tambechristian/Zulu_A7/Zulu_Altium_VS_Code/docs/power_budget.md

# Zulu A7 power budget

Source: zulu_a7.sch as imported (Imported zulu_a7.PrjPcb), datasheets in Datasheet/. Generated by tools/power_budget.py with --fpga-int 250 --fpga-aux 15 --fpga-io 30 --header 0.

Power comes in as USB VBUS into U8, a TI bq24232 charger and power-path manager whose OUT regulates VU at 4.4 V and caps the input at 495 mA, charging the LiPo on X4 at up to 244 mA with what is left (the battery supplements peaks and runs the board alone at VBAT - 60 mV). The +5V-INPUT pin with D2 and D3 went on 2026-09-09, so the charger is the only way in. VU feeds three fixed SC189 bucks, U5 (3.3 V), U6 (1.8 V) and U7 (1.0 V), 1.5 A each at 2.5 MHz, enables tied to VU, so all three rails soft-start together when VU appears; UG483 requires no order between VCCINT, VCCAUX and VCCO.

## VCC3V3 = 3.3 V on U5 SC189Z (1.5 A)

| Consumer | typ mA | max mA | Source |
|---|---:|---:|---|
| U2 FT2232HL core via VREGIN (Icc1) | 70 | 70 | FT2232H DS Table 5.2, 70 mA |
| U2 FT2232HL USB PHY (Iccphy, high speed) | 30 | 60 | FT2232H DS Table 5.4, 30 typ / 60 max |
| U2 FT2232HL VCCIO switching | 10 | 20 | ASSUMED, 3.3 V I/O cells at JTAG/UART rates |
| U3 SDRAM AS4C32M16SB-7TCN | 100 | 150 | IDD1 110, IDD4 120, IDD5 150 (refresh), IDD2N 80 standby (Rev 1.4); the -6TIN was 120/124/160 until 2026-09-08 |
| U4 W25Q128JV flash (quad read 104 MHz / program) | 12 | 25 | ICC3 12 typ 20 max; ICC5 program 25 max |
| X3 microSD card | 60 | 200 | SD spec: ~60 typ, 200 max at 3.3 V for a high-speed card |
| U10 93LC46B EEPROM | 1 | 2 | read 1 mA, write 2 mA max |
| Q1 ECS-3225SMV 12 MHz oscillator | 6 | 10 | ECS-3225SMV sheet: 6 typ / 10 mA max at 15 pF (was ASEM1 7/15 until 2026-09-08) |
| U1 VCCO banks 0/14/16/34/35 (28 balls) static | 5 | 5 | DS181 ICCOQ, about 1 mA per bank |
| U1 VCCO dynamic (SDRAM bus, header, LED sink path) | 30 | 90 | ASSUMED; about 1.6 mA per toggling pin at 100 MHz, 10 pF |
| LD0 RGB (R80 33, R81 330, R82 33) + LD1/LD2 (330) + LD5 (680) | 8 | 22 | VF from the Everlight 19-337 sheet: red 2.05 typ / 2.4 max, green and blue 3.2 typ / 3.7 max V (VS NRD8 was 2.0-2.4 / 3.3-3.8 until 2026-09-08) |
| pull-ups when driven low (6 x 4.7k, 12 x 10k) | 2 | 8 | R1, R2, R6, R7, R34, R35, R90-R99, R19, R20, R23 |
| J1 Pmod pins 6/12 and X2 pin 18 +3.3V to header | 0 | 0 | external, user allowance |
| **Total** | **334** | **662** | channel limit 1500 mA |
| Headroom | 1166 | 838 | ok |

## VCC1V8 = 1.8 V on U6 SC189L (1.5 A)

| Consumer | typ mA | max mA | Source |
|---|---:|---:|---|
| U1 VCCAUX quiescent (H13, J13) | 22 | 22 | DS181 Table 7, ICCAUXQ 22 mA |
| U1 VCCAUX dynamic (MMCM, config, I/O aux) | 15 | 30 | ASSUMED; Vivado report_power |
| U1 VCCADC via L7 (XADC on, AIN15/AIN16 used) | 12 | 25 | DS181 ICCADC 25 mA max |
| U1 VCCBATT (C9) | 0 | 0 | tied to VCC1V8, no battery: negligible |
| X2 pin 19 +1.8V to header | 0 | 0 | external, user allowance |
| **Total** | **49** | **77** | channel limit 1500 mA |
| Headroom | 1451 | 1423 | ok |

## VCC1V0 = 1.0 V on U7 SC189A (1.5 A)

| Consumer | typ mA | max mA | Source |
|---|---:|---:|---|
| U1 VCCINT quiescent (6 balls) | 95 | 95 | DS181 Table 7, XC7A35T ICCINTQ 95 mA typ at 85 C junction |
| U1 VCCINT dynamic | 250 | 250 | ASSUMED design load; replace with Vivado report_power |
| U1 VCCBRAM (2 balls) quiescent + dynamic | 22 | 22 | DS181 ICCBRAMQ 2 mA; dynamic assumed |
| X2 pin 20 +1.0V to header | 0 | 0 | external, user allowance |
| **Total** | **367** | **367** | channel limit 1500 mA |
| Headroom | 1133 | 1133 | ok |

## Power-on requirement (DS181 Table 9, XC7A35T)

The supplies must deliver the quiescent current plus an inrush allowance while the FPGA powers up, before anything is configured:

| Rail | Requirement | This board | ok |
|---|---|---:|---|
| VCC1V0 | ICCINTQ + 120 + ICCBRAMQ + 60 | 277 mA | ok (channel 1500 mA) |
| VCC1V8 | ICCAUXQ + 40 | 62 mA | ok (channel 1500 mA) |
| VCC3V3 | ICCOQ + 40 mA per bank x 5 banks, plus the rest of the rail at rest | 362 mA | ok (channel 1500 mA) |

## Input from USB

VU = 4.40 V, the bq24232 OUT regulation while USB is present (the charger is an LDO from the 5 V port). Input power per rail is Vout x Iout / efficiency, efficiency read from the SC189 datasheet's SOT23-5 curves at 5 V in (p6).

| Rail | typ W in | max W in | efficiency |
|---|---:|---:|---:|
| VCC3V3 | 1.22 | 2.43 | 90% |
| VCC1V8 | 0.11 | 0.18 | 78% |
| VCC1V0 | 0.45 | 0.45 | 81% |
| **USB current at 4.40 V** | **409 mA** | **697 mA** | bq24232 input limit 495 mA; USB allows 500 mA configured, 100 mA before enumeration |

- Typical use draws about 409 mA through the charger: inside the 495 mA input limit, leaving about 86 mA of the 244 mA charge current for the battery while the board runs; the full 244 mA flows when the board idles.
- The simultaneous worst case wants about 697 mA: over the charger's input limit, so the excess comes from the battery in supplement mode; with no battery fitted VU sags to the DPPM point and the board browns out under that load.
- All three rails start as soon as VBUS appears and the FPGA configures from flash immediately, so the board is above the 100 mA unconfigured limit before the FT2232H enumerates. Hosts tolerate this in practice; FT-PWREN# reaches the FPGA (P17) if you ever want to hold heavy loads off until enumeration.
- VU, which is the charger's OUT, carries C78 (10 uF) plus the three SC189 input caps C147-C149 (10 uF each; the datasheet wants at least 4.7 uF effective at every VIN pin): 40 uF nominal, roughly 25 uF effective at 5 V. The USB 2.0 limit for bulk capacitance seen at attach is 10 uF (50 uC of inrush). The bq24232 sits between the port and that capacitance and limits inrush by its start-up sequence; the datasheet allows 4.7-47 uF on OUT, so the 40 uF is inside its window. On battery alone the SC189 3.3 V buck keeps regulation down to about 3.45 V of battery (VU = VBAT - 60 mV); the 1.8 V and 1.0 V rails run to the pack's cut-off.

## Thermal, still air, first order

| Part | P typ W | P max W | thJA C/W | rise typ C | rise max C |
|---|---:|---:|---:|---:|---:|
| U1 XC7A35T CPG236 | 0.57 | 0.82 | 24.8 | 14 | 20 |
| U5 SC189Z (1.5 A) for VCC3V3 | 0.12 | 0.24 | 90 | 11 | 22 |
| U6 SC189L (1.5 A) for VCC1V8 | 0.02 | 0.04 | 90 | 2 | 4 |
| U7 SC189A (1.5 A) for VCC1V0 | 0.09 | 0.09 | 90 | 8 | 8 |
| U2 FT2232HL (DS Table 5.7) | 0.36 | 0.49 | 37.66 | 14 | 19 |
| U3 SDRAM (thJA assumed) | 0.33 | 0.53 | 45 | 15 | 24 |
| U8 bq24232 (DS 7.4, path + charge) | 0.36 | 0.61 | 44.5 | 16 | 27 |

The FPGA stays well under its 85 C commercial junction limit. The SOT23-5 regulators are the warm parts now: the 3.3 V one dissipates about 0.12 W typical and up to 0.25 W at the datasheet maxima, which at the datasheet's 90 C/W (SOT23-5 on a 10x10 mm 2-layer 1 oz test board) is an 11-22 C rise. Figure 3 of the SC189 sheet rates the SOT23-5 for the full 1.5 A at 3.3 V out up to about 65 C ambient, so no derating applies here. Give the GND pin and the LX/VOUT copper a pour anyway; the 2x2 mm MLPD-UT6 version (SC189xULTRT, 60 C/W) is the fallback if the board must run hot.

## Findings

1. **No rail is near its regulator limit any more.** Each SC189 gives 1.5 A; VCC3V3 uses under a quarter of that in typical use and under half at the datasheet maxima, VCC1V0 a quarter, VCC1V8 a twentieth. The header and Pmod +3.3V pins can take several hundred milliamps when the board runs from USB with a charged battery supplementing.
2. **The bq24232 input limit is the ceiling on USB.** The charger holds the port at 495 mA whatever the board does; typical use fits, the datasheet-maximum case is served by the battery in supplement mode, the only other source now that the +5V-INPUT pin is gone.
3. **VCC1V8 is lightly loaded**, well under 100 mA even with the XADC running.
4. **USB alone covers typical use** at about 409 mA through the charger, with about 86 mA left for charging. The simultaneous worst case (697 mA) needs the battery in supplement mode; there is no other input since the +5V-INPUT pin went on 2026-09-09.
5. **Green and blue of LD0 may not light.** Their forward voltage is 3.2 V typical and 3.7 V maximum per the Everlight 19-337 sheet (3.3-3.8 V on the VS NRD8 it replaced on 2026-09-08), and the FPGA sinks them from a 3.3 V supply through 33 ohm, leaving no headroom; only the red (2.0-2.4 V) has margin. Expect dim or dark green/blue unless the parts fall at the low end of VF. Not a power problem, but it fell out of the LED current estimate.
6. **Sequencing is gone by design.** Every SC189 EN is tied to VU, so the three rails soft-start together. UG483 recommends VCCINT, VCCBRAM, VCCAUX, VCCO but requires no order and allows simultaneous ramps. The old LTC3569 EN_BIAS network went with it; it was copied from the Cmod A7 rev B, which Digilent shipped, so it evidently works in practice, but it holds the gated enables at 0.65-0.8 V, below the LTC3569 guaranteed 1.2 V high level, and Q3 pulls them low once VCC1V0 is up.
7. **The rails carry far more capacitance than the SC189 datasheet allows at start-up.** Page 19 says total output capacitance should not exceed 30 uF to avoid start-up problems: the fixed 100 us soft-start (current limit stepped 20/25/40/100 % of 2 A, 20 us each) delivers only 40-75 uC, after which the part runs at its 2 A limit and, after 32 cycles over the limit, folds back to 50-110 mA (Figure 5) until the load falls below that. UG483 Table 2-2 requires 100 uF on VCCINT, 47 uF on VCCBRAM, 47 uF on VCCAUX and 47 uF per VCCO group for this FPGA, so the sheet has 165 uF nominal on VCC1V0, 167 uF on VCC3V3 and 72 uF on VCC1V8 (about 150, 90 and 60 uF after DC bias), needing 150, 300 and 110 uC. Every rail therefore finishes its ramp in current limit or foldback, and a load that draws more than the foldback current before the rail is up (the FPGA's VCCINT power-on current is about 200 mA, the FT2232H on 3.3 V about 70 mA) could hold it down. A newer Cmod A7 revision runs three SC189s into this same FPGA (the source is the user's photo of that board; the rev B.1 schematic on disk still shows the LTC3569), which suggests it works in practice, but it is the one datasheet limit this design does not meet: scope the three rails at power-on on the first board. If a rail hangs, the fixes are a regulator with a soft-start pin in the same role (TPS62130/TPS62823 class) or staggering the enables with RC delays so the rails do not all draw from VU at once.
