tambechristian/Zulu_A7/Altium_backup/docs/sdram_bus_widths.md

# SDRAM bus on L3/L4 — width, spacing and what the bus actually needs, 2026-09-14

**Status: APPLIED AND PROVEN, 2026-09-15.** Three analyses (signal integrity,
routability, fab and yield), each adversarially refuted, then a judge — 1.28 M tokens, all
numbers below survived refutation from the files or are marked general knowledge. The
implementation is `SetSdramRules` in `tools/ZuluSetup.pas`; `tools/verify_widths.py` carries
the targets.

## What the bus needs — and it is not 50 Ω
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
