tambechristian/Zulu_A7/Zulu_Altium_VS_Code_HDI_Optimized/jlcpcb_hdi_optimized_cost_vs_regular.png

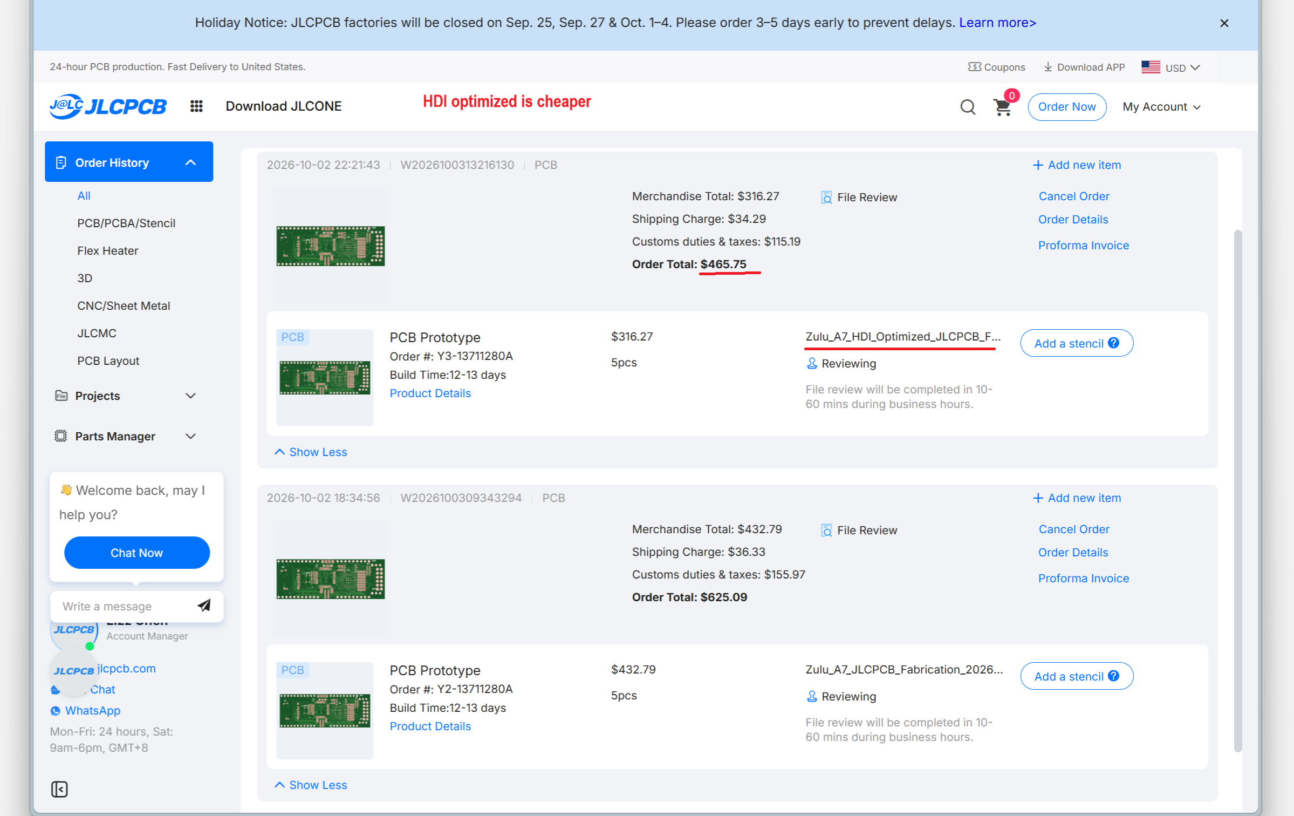
Zulu_Altium_VS_Code_HDI_Optimized/jlcpcb_hdi_optimized_cost_vs_regular.png
