tambechristian/Zulu_A7/Zulu_Altium_VS_Code_HDI_Optimized/pcbway_cost.png

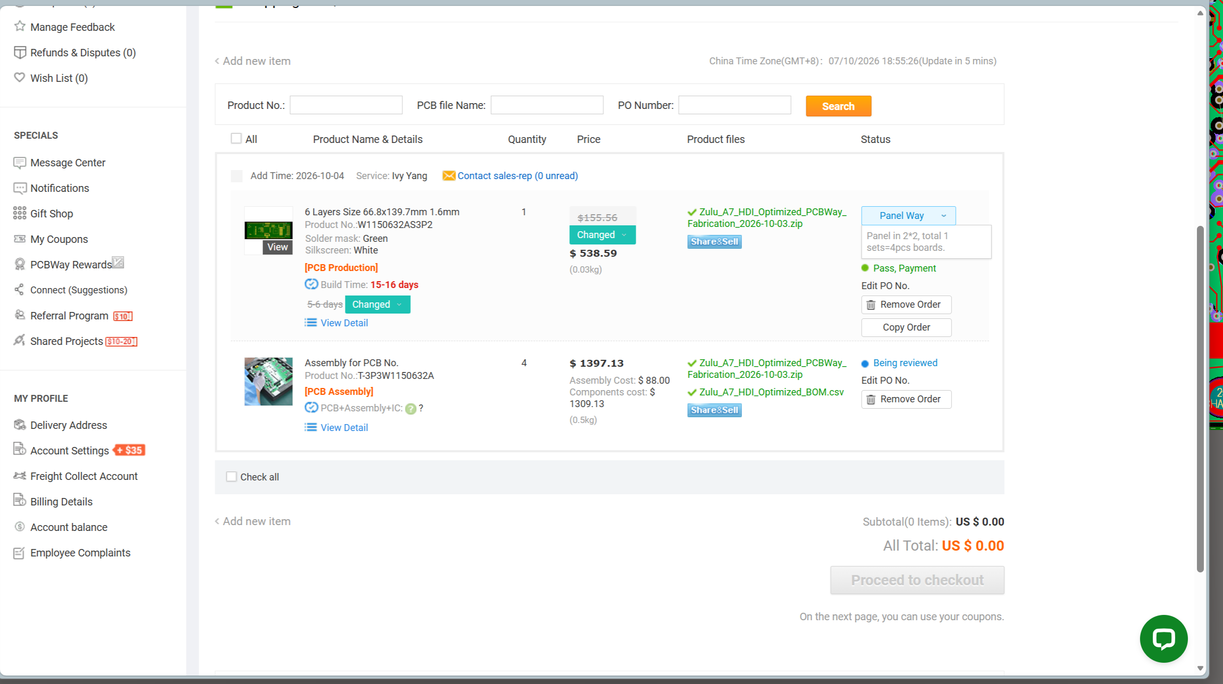
Zulu_Altium_VS_Code_HDI_Optimized/pcbway_cost.png
