tambechristian/Zulu_A7/Claude_Fable/tools/plane_islands.py

# -*- coding: utf-8 -*-
"""Does an inner plane pour actually reach every through object of its net?

    python tools/plane_islands.py [board.brd] [--layer 2] [--net GND]
    python tools/plane_islands.py zulu_a7.brd --layer 5 --net VCC3V3

WHY. check_connectivity treats a <polygonpour> on L2 or L5 as SOLID: every via
and plated pad of the net that crosses the layer is taken as one piece. That is
what a plane is for, but it is an assumption, and two things on this board can
break it. Seven signals were routed ON the plane layers with laser vias, and
every one of their traces is a slot cut through the copper. And the BGA moat
puts foreign vias at 0.39 mm centres, whose antipads overlap into a wall. A via
of the plane's own net standing inside such a slot or wall has copper around it
that is not the plane. Fusion's DRC reports exactly that as an "Air Wire" that
Ratsnest never showed, which is where the 63-against-41 gap came from.

HOW. Rasterise the pour outline. A pour centreline must keep `isolate` from
every foreign object and the copper it lays is `width` wide, so the region a
centreline may occupy is everything at least isolate + width/2 from foreign
copper. Flood that region into pieces. An own via or plated pad is reached by a
piece if a cell of that piece lies within its land radius + width/2 of it, so
the pour's copper edge touches the land. Report every own object that no piece
reaches (isolated) and every one reached only by a piece other than the main
plane (on an island).

Foreign plated pads are modelled at their full drawn diameter on the inner
layer, which is conservative: Eagle draws only the restring annulus there.
"""

import collections
import io
import math
import os
import re
import sys

sys.path.insert(0, os.path.dirname(os.path.abspath(__file__)))
import escape as E   # noqa: E402
import geom as G     # noqa: E402

ROOT = os.path.dirname(os.path.dirname(os.path.abspath(__file__)))
RASTER = 0.05


def arg(name, default):
    if name in sys.argv:
        return sys.argv[sys.argv.index(name) + 1]
    return default


def via_span(attrs):
    first, last = (int(v) for v in attrs.get("extent", "1-16").split("-"))
    return min(first, last), max(first, last)


def analyse(board, layer, net, log=print, grid=None):
    """Raster the pour; report. With `grid` = (x0, y0, W, H) the raster is
    laid on the caller's grid (RASTER step) so its labels can be used as a
    routing layer. Returns a dict, or None if the net has no pour there:
        isolated, islanded   lists of (kind, x, y)
        reached              set of (x, y) rounded to 3 places, own objects
                             the main piece reaches
        label, main, W, H, x0, y0, S     the raster itself
    """
    sig = re.search(r"<signals>(.*)</signals>", board, re.S).group(1)
    signals = {}
    for m in re.finditer(r'<signal name="([^"]+)"[^>]*>(.*?)</signal>', sig, re.S):
        signals[m.group(1)] = m.group(2)
    own_body = signals.get(net, "")
    pm = re.search(r'<polygonpour layer="%d"([^>]*)>(.*?)</polygonpour>'
                   % layer, own_body, re.S)
    if not pm:
        log("  ****  %s has no pour on layer %d" % (net, layer))
        return None
    attrs = dict(re.findall(r'(\w+)="([^"]*)"', pm.group(1)))
    isolate = float(attrs.get("isolate", "0.25"))
    width = float(attrs.get("width", "0.1524"))
    verts = [(float(x), float(y)) for x, y in
             re.findall(r'<vertex x="([-\d.]+)" y="([-\d.]+)"', pm.group(2))]
    x0, x1 = min(v[0] for v in verts), max(v[0] for v in verts)
    y0, y1 = min(v[1] for v in verts), max(v[1] for v in verts)
    keep = isolate + width / 2.0

    # own entries: (kind, key x, key y, land radius, sample points). A pad or
    # via is one sample at its centre; an own wire on the layer is sampled
    # along its length, keyed by its first point, because Fusion pours the
    # copper straight over its own wires and they become part of the plane.
    circles, rects, own = [], [], []
    for onet, x, y, hx, hy, side in E.board_copper(board, skip=()):
        if side != 0 and side != layer:
            continue
        if onet == net:
            own.append(("pad", x, y, max(hx, hy), [(x, y)]))
        else:
            rects.append((x, y, hx, hy))
    segs = []
    for onet, body in signals.items():
        for vm in re.finditer(r"<via\s([^>]*)>", body):
            a = dict(re.findall(r'(\w+)="([^"]*)"', vm.group(1)))
            if "x" not in a:
                continue
            lo, hi = via_span(a)
            if not lo <= layer <= hi:
                continue
            drill = float(a.get("drill", "0.2"))
            if "diameter" in a:
                dia = float(a["diameter"])
            else:
                dia = drill + 2 * max(drill * 0.25, 0.05)
            x, y = float(a["x"]), float(a["y"])
            if onet == net:
                own.append(("via", x, y, dia / 2.0, [(x, y)]))
            else:
                circles.append((x, y, dia / 2.0))
        for w in re.finditer(
                r'<wire x1="([-\d.]+)" y1="([-\d.]+)" x2="([-\d.]+)"'
                r' y2="([-\d.]+)" width="([\d.]+)" layer="(\d+)"', body):
            if int(w.group(6)) != layer:
                continue
            xa, ya, xb, yb, wd = (float(v) for v in w.groups()[:5])
            if onet == net:
                own.append(("wire", xa, ya, wd / 2.0,
                            [(sx, sy) for sx, sy, sr in G.sample((xa, ya), (xb, yb), wd / 2.0, step=RASTER)]))
            else:
                segs.append(((xa, ya), (xb, yb), wd / 2.0))

    S = RASTER
    if grid is None:
        W = int((x1 - x0) / S) + 1
        H = int((y1 - y0) / S) + 1
        N = W * H
        core = bytearray(b"\x01") * N
    else:
        gx0, gy0, W, H = grid
        N = W * H
        core = bytearray(N)
        for j in range(H):
            y = gy0 + j * S
            if not y0 - 1e-9 <= y <= y1 + 1e-9:
                continue
            i0 = max(0, int(math.ceil((x0 - gx0) / S - 1e-9)))
            i1 = min(W - 1, int(math.floor((x1 - gx0) / S + 1e-9)))
            if i1 >= i0:
                core[j * W + i0:j * W + i1 + 1] = b"\x01" * (i1 - i0 + 1)
        x0, y0 = gx0, gy0

    def ci(x):
        return int(round((x - x0) / S))

    def cj(y):
        return int(round((y - y0) / S))

    def block_circle(cx, cy, r):
        rad = r + keep
        rr = int(rad / S) + 2
        i0, j0 = ci(cx), cj(cy)
        for i in range(max(0, i0 - rr), min(W, i0 + rr + 1)):
            dx = x0 + i * S - cx
            for j in range(max(0, j0 - rr), min(H, j0 + rr + 1)):
                dy = y0 + j * S - cy
                if dx * dx + dy * dy < rad * rad:
                    core[j * W + i] = 0
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
